Buddinski88/R2-D2-Modular-body-backpack/images/documentation/Body-Adapterplate-glued.png

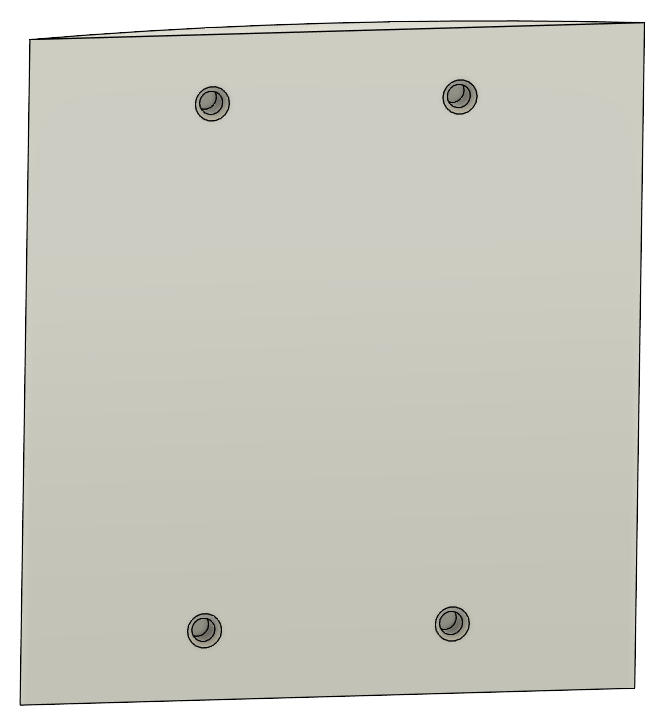
images/documentation/Body-Adapterplate-glued.png
