Buddinski88/R2-D2-Modular-body-backpack/images/documentation/fullsize/Adapter-Hall-Sensor-V2.png

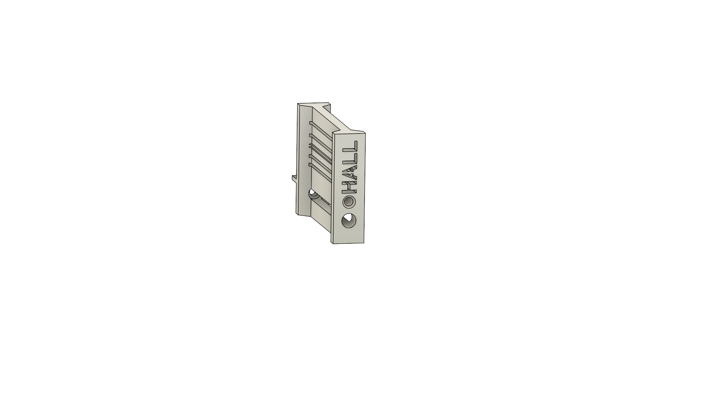
images/documentation/fullsize/Adapter-Hall-Sensor-V2.png
