Buddinski88/R2-D2-Modular-body-backpack/images/documentation/fullsize/Frame.png

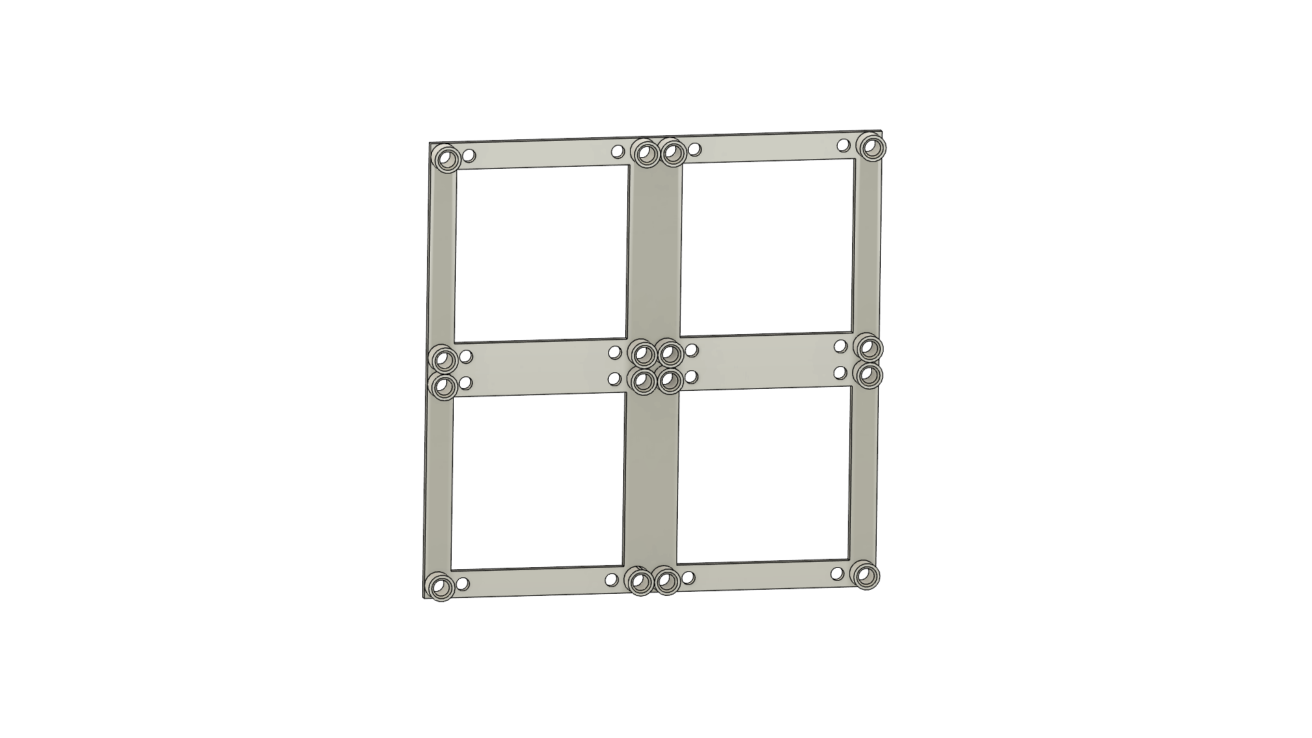
images/documentation/fullsize/Frame.png
