Buddinski88/R2-D2-Modular-body-backpack/images/documentation/fullsize/Panel-Buck-Converter_fixed_5V_d4x4.png

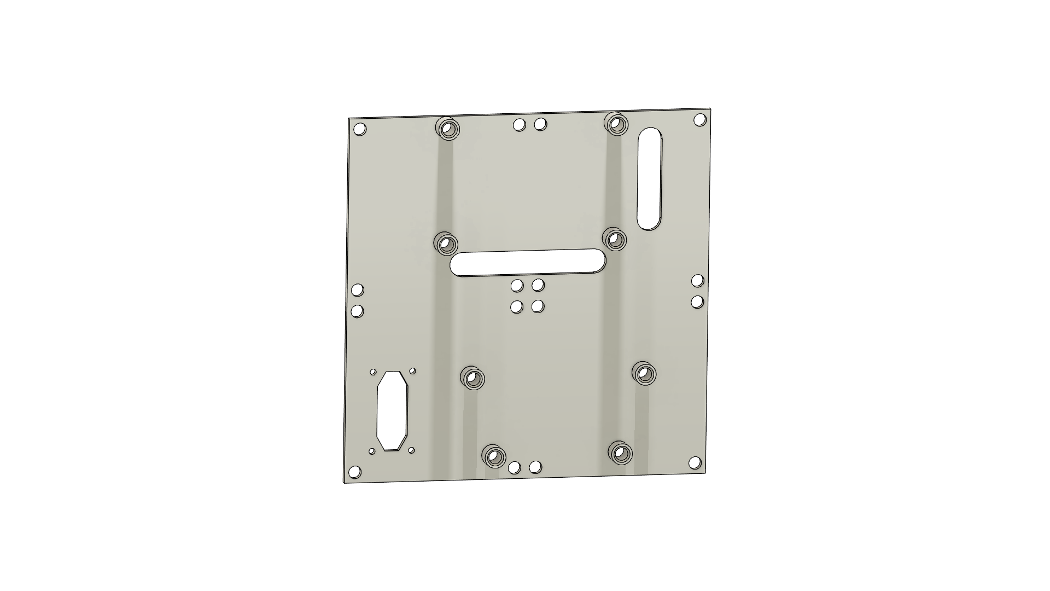
images/documentation/fullsize/Panel-Buck-Converter_fixed_5V_d4x4.png
